VasanthKarthikeyan/Self-Balancing-Robot-/minor_proj.kicad_sch

## KiCad design minor_proj.kicad_sch (2026-04-28)

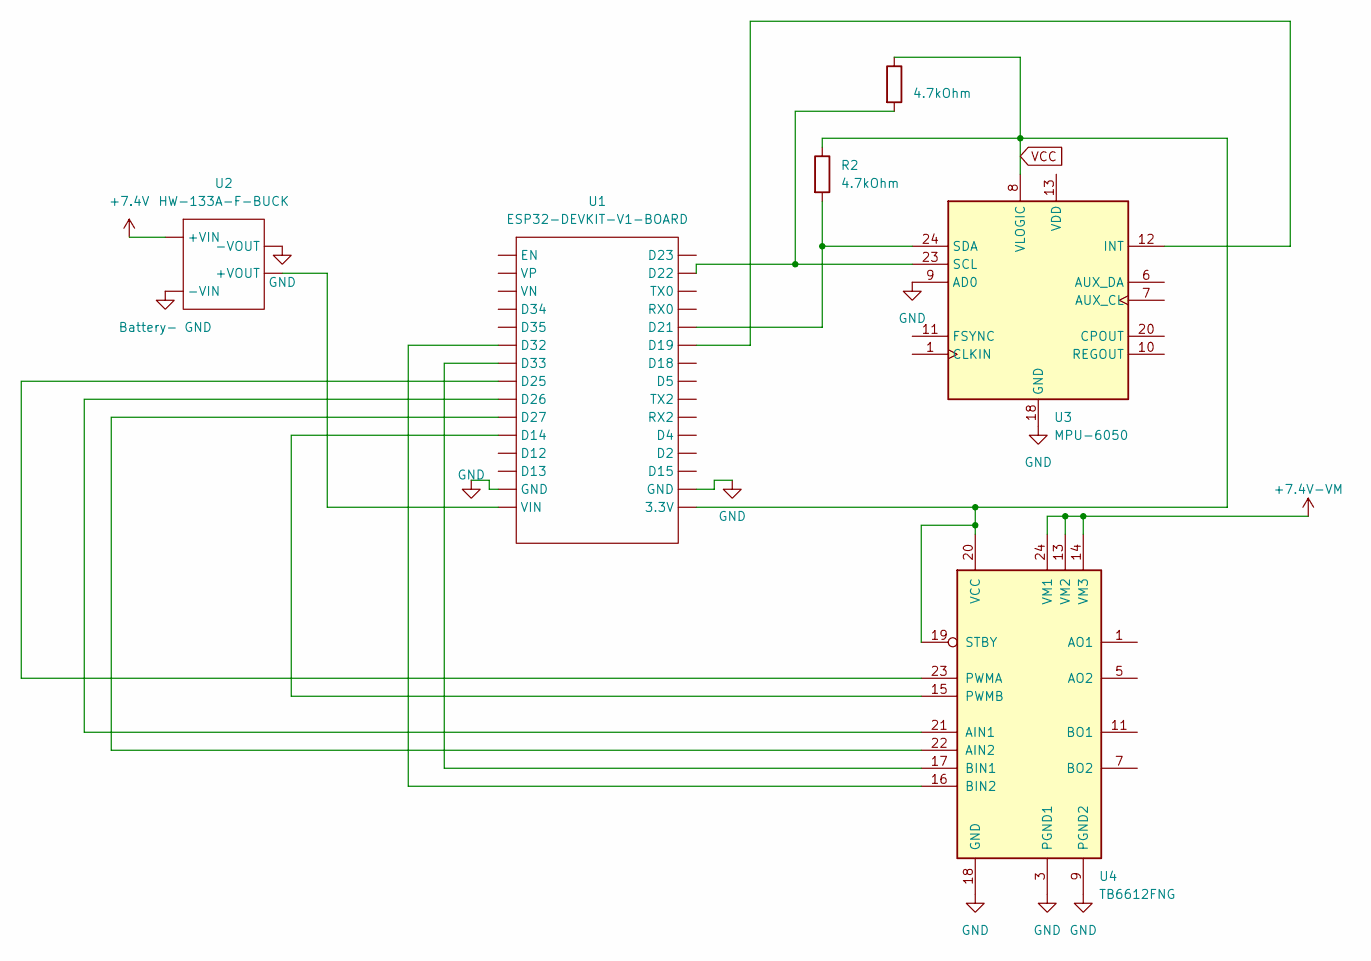
[picture p4: schematic minor_proj.kicad_sch]

Parts:
R1, R2: 4.7kOhm
U1: ESP32-DEVKIT-V1-BOARD
U2: HW-133A-F-BUCK
U3: MPU-6050; InvenSense_QFN-24_4x4mm_P0.5mm
U4: TB6612FNG; SSOP-24_5.3x8.2mm_P0.65mm

Connections:
+7.4V: U2.
+7.4V-VM: U4.13 (VM2), U4.14 (VM3), U4.24 (VM1)
Battery- GND: U2.
GND: U1., U2., U3.9 (AD0), U3.18 (GND), U4.3 (PGND1), U4.4 (PGND1), U4.9 (PGND2), U4.10 (PGND2), U4.18 (GND)
unnamed: R1.2, U1., U3.23 (SCL)
unnamed: R2.2, U1., U3.24 (SDA)
unnamed: U1., U2., U3.12 (INT), U4.15 (PWMB), U4.16 (BIN2), U4.17 (BIN1), U4.21 (AIN1), U4.22 (AIN2), U4.23 (PWMA)
unnamed: U4.1 (AO1), U4.2 (AO1)
unnamed: U4.5 (AO2), U4.6 (AO2)
unnamed: U4.7 (BO2), U4.8 (BO2)
unnamed: U4.11 (BO1), U4.12 (BO1)
VCC: R1.1, R2.1, U1., U3.8 (VLOGIC), U4.19 (STBY), U4.20 (VCC)
